7FM/DryNoMore/server/telegram_bot/src/telegram_bot.cpp

#include <iostream>
#include <tgbot/tgbot.h> // https://github.com/reo7sp/tgbot-cpp
#include <vector>

#include "telegram_bot.hpp"
#include "telegram_bot_keyboards.hpp"
#include "telegram_bot_utils.hpp"

void runDryNoMoreTelegramBot(const std::string &token,
                             const std::set<std::int64_t> &userWhitelist,
                             std::set<std::int64_t> &broadcastChats,
                             StateWrapper &state, ts_queue<Message> &msgQueue,
                             const std::atomic<bool> &running) {
  TgBot::Bot bot(token);

  std::vector<TgBot::BotCommand::Ptr> commands;
  std::vector<TgBot::EventBroadcaster::MessageListener> commandHandler;

  Settings settingSnapshot;
  auto &api = bot.getApi();

  auto addCommand = [&](const std::string &command,
                        const std::string &description,
                        TgBot::EventBroadcaster::MessageListener handler) {
    TgBot::BotCommand::Ptr cmd(new TgBot::BotCommand);
    cmd->command = command;
    cmd->description = description;
    commands.push_back(std::move(cmd));
    commandHandler.push_back(std::move(handler));
  };

  addCommand("start", "init conversation", [&](TgBot::Message::Ptr message) {
    api.sendMessage(message->chat->id, "Howdy!");
  });

  KeyboardManager menus(settingSnapshot, [&settingSnapshot, &state]() {
    auto &set = state.settingsWrap;
    std::scoped_lock lock(set.mut);
    // Move snapshot settings to actual settings!
    std::memcpy(&set.settings, &settingSnapshot, sizeof(settingSnapshot));
  });

  addCommand("edit", "edit the DryNoMore irrigation settings",
             [&](TgBot::Message::Ptr message) {
               const auto &set = state.settingsWrap;
               bool valid = false;
               {
                 std::scoped_lock lock(set.mut);
                 if ((valid = set.valid)) {
                   std::memcpy(&settingSnapshot, &set.settings,
                               sizeof(settingSnapshot));
                 }
               }

               if (valid) {
                 api.sendMessage(message->chat->id,
                                 generateSettingsTable(settingSnapshot), false,
                                 0, menus.init(), "Markdown");
               } else {
                 std::string response =
                     "Settings are not yet synchronized!\nPlease wait for the "
                     "next status report!";
                 api.sendMessage(message->chat->id, response);
               }
             });

  // Register callbacks!
  auto &broadcaster = bot.getEvents();

  for (size_t i = 0; i < commands.size(); ++i) {
    broadcaster.onCommand(
        commands[i]->command, [&, i](TgBot::Message::Ptr message) {
          if (!userWhitelist.contains(message->from->id)) {
            api.sendMessage(message->chat->id,
                            "Access denied! Go get your own bot! User ID: " +
                                std::to_string(message->from->id));
            return;
          }
          // save the chat ID!
          broadcastChats.insert(message->chat->id);

          commandHandler[i](message);
        });
  }

  menus.registerActions(api, broadcaster);

  // Set my commands
  api.setMyCommands(commands);

  TgBot::TgLongPoll longPoll(bot);
  while (running.load(std::memory_order_relaxed)) {
    // check if the status was not yet published & send update
    {
      std::unique_lock lock(state.statusWrap.mut);

      if (state.statusWrap.unpublished) {
        state.statusWrap.unpublished = false;
        Status statusCopy;
        std::memcpy(&statusCopy, &state.statusWrap.status, sizeof(statusCopy));
        lock.unlock();

        std::string statusUpdate = generateStatusTable(statusCopy);
        for (std::int64_t chat : broadcastChats) {
          api.sendMessage(chat, statusUpdate, false, 0,
                          std::make_shared<TgBot::GenericReply>(), "Markdown");
        }
      }
    }

    // send all messages in the message queue
    while (running.load(std::memory_order_relaxed) && !msgQueue.empty()) {
      if (auto msg = msgQueue.limited_wait_for_pop()) {
        const char *msgPrefix = nullptr;
        switch (msg->msgType) {
          case INFO_MSG: {
            msgPrefix = "INFO: ";
            break;
          }
          case WARN_MSG: {
            msgPrefix = "WARNING: ";
            break;
          }
          case ERR_MSG: {
            msgPrefix = "ERROR: ";
            break;
          }
          case FAILURE_MSG: {
            msgPrefix = "HARDWARE FAILURE: ";
            break;
          }
          default: {
            std::cerr << "Error invalid message in msgQueue!" << std::endl;
            continue;
          }
        }
        std::string message = msgPrefix + msg->msg;

        for (std::int64_t chat : broadcastChats) {
          api.sendMessage(chat, message, false, 0,
                          std::make_shared<TgBot::GenericReply>(), "Markdown");
        }
      }
    }

    // Handle user input
    try {
      longPoll.start();
    } catch (const TgBot::TgException &e) {
      std::cerr << "telegram bot error: " << e.what() << std::endl;
    } catch (const boost::system::system_error &wtf) {
      std::cerr << "boost system error: " << wtf.what() << std::endl;
    } catch (const std::exception &dafuq) {
      std::cerr << "std::exception: " << dafuq.what() << std::endl;
    }
  }
}
