7FM/DryNoMore/server/telegram_bot/src/telegram_bot_utils.cpp

#include <sstream>

#include "telegram_bot_utils.hpp"
#include "types.hpp"

static size_t findMaxStringLineSize(const std::string &s) {
  size_t max = 0;
  auto it = s.find('\n');
  if (it != std::string::npos) {
    max = std::max(it, findMaxStringLineSize(s.substr(it + 1)));
  } else {
    max = s.size();
  }

  return max;
}

static void printMultiLineRow(std::ostream &stream,
                              const std::vector<size_t> &maxChars,
                              const std::vector<std::string> &row,
                              const std::vector<bool> &printLeftWhitespace,
                              const std::vector<bool> &printRightWhitespace) {
  std::vector<std::string> newRow;
  std::vector<std::string> nextRow;
  const std::vector<std::string> *currentRow = &row;

  do {
    stream << "|";
    for (size_t i = 0; i < maxChars.size(); ++i) {
      if (printLeftWhitespace.empty() || printLeftWhitespace[i]) {
        stream << ' ';
      }
      auto old = stream.width(maxChars[i]);
      const auto &s = (*currentRow)[i];

      // Split up row if it contains newlines
      auto it = s.find('\n');
      if (it != std::string::npos) {
        // Fill with empty strings up to i
        newRow.resize(i);

        stream << s.substr(0, it);
        newRow.push_back(s.substr(it + 1));
      } else {
        stream << s;
      }

      stream.width(old);
      stream << (printRightWhitespace.empty() || printRightWhitespace[i] ? " |"
                                                                         : "|");
    }
    stream << '\n';

    std::swap(nextRow, newRow);
    newRow.clear();

    if (!nextRow.empty()) {
      nextRow.resize(maxChars.size());
    }
    currentRow = &nextRow;
  } while (!currentRow->empty());
}

std::string generateTable(const std::vector<std::vector<std::string>> &table,
                          const std::vector<bool> &printLeftWhitespace,
                          const std::vector<bool> &printRightWhitespace) {

  if (table.empty()) {
    return "";
  }

  std::vector<size_t> maxChars;
  maxChars.reserve(table[0].size());

  size_t totalWidth = 1;
  for (size_t i = 0; i < table[0].size(); ++i) {
    size_t max = 0;
    for (auto &row : table) {
      max = std::max(max, findMaxStringLineSize(row[i]));
    }
    totalWidth +=
        max + 1 +
        (printLeftWhitespace.empty() || printLeftWhitespace[i] ? 1 : 0) +
        (printRightWhitespace.empty() || printRightWhitespace[i] ? 1 : 0);
    maxChars.push_back(max);
  }

  std::stringstream ss;
  ss << "```\n";

  auto print_break = [&] {
    ss.width(totalWidth);
    ss.fill('-');
    ss << '-' << '\n';
    ss.fill(' ');
  };

  ss.setf(std::ios::left, std::ios::adjustfield);
  print_break();
  printMultiLineRow(ss, maxChars, table[0], printLeftWhitespace,
                    printRightWhitespace);
  print_break();
  for (size_t i = 1; i < table.size(); ++i) {
    printMultiLineRow(ss, maxChars, table[i], printLeftWhitespace,
                      printRightWhitespace);
  }
  print_break();

  ss << "```\n";
  return ss.str();
}

std::string generateWaterSettingsTable(const Settings &settings) {
  std::vector<std::vector<std::string>> table;
  table.reserve(1 + 2);

  std::vector<bool> printLeftWhitespace = {false, true, true, true, true};
  std::vector<bool> printRightWhitespace = {false, true, true, false, false};
  std::vector<std::string> row{"ID", "Min\nVal", "Max\nVal", "Warn\nThres",
                               "Empty\nThres"};
  table.push_back(std::move(row));

  for (int i = 0; i < 2; ++i) {
    row = {"W" + std::to_string(i + 1),
           std::to_string(
               settings.sensConfs[(MAX_MOISTURE_SENSOR_COUNT) + i].minValue),
           std::to_string(
               settings.sensConfs[(MAX_MOISTURE_SENSOR_COUNT) + i].maxValue),
           std::to_string(settings.waterLvlThres[i].warnThres) + " %",
           std::to_string(settings.waterLvlThres[i].emptyThres) + " %"};
    table.push_back(std::move(row));
  }

  return "Water-level Sensor Settings:\n" +
         generateTable(table, printLeftWhitespace, printRightWhitespace);
}

std::string generateMoistSettingsTable(const Settings &settings) {
  std::vector<std::vector<std::string>> table;
  table.reserve(1 + settings.numPlants);

  std::vector<bool> printLeftWhitespace = {false, true,  true,
                                           true,  false, true};
  std::vector<bool> printRightWhitespace = {false, true,  true,
                                            false, false, true};
  std::vector<std::string> row{"ID",          "Min\nVal", "Max\nVal",
                               "Moist\nGoal", "Wat\nSen", "Skp"};
  table.push_back(std::move(row));

  for (int i = 0; i < settings.numPlants; ++i) {
    uint8_t sensorIdx =
        (settings.moistSensToWaterSensBitmap[i / 8] >> (i & 7 /*aka mod 8*/)) &
        0x01;
    uint8_t skip = (settings.skipBitmap[i / 8] >> (i & 7 /*aka mod 8*/)) & 0x01;
    row = {"P" + std::to_string(i + 1),
           std::to_string(settings.sensConfs[i].minValue),
           std::to_string(settings.sensConfs[i].maxValue),
           std::to_string(settings.targetMoisture[i]) + " %",
           sensorIdx ? "W2" : "W1",
           skip ? "yes" : "no"};
    table.push_back(std::move(row));
  }

  std::string moistureSensorSettings(
      generateTable(table, printLeftWhitespace, printRightWhitespace));
  table.clear();

  printLeftWhitespace = {false, true, true, true, true};
  printRightWhitespace = {false, false, false, false, false};
  row = {"ID", "Burst\nLen", "Burst\nDelay", "Max #\nBursts", "Tick\nb/w\nWat"};
  table.push_back(std::move(row));

  for (int i = 0; i < settings.numPlants; ++i) {
    row = {"P" + std::to_string(i + 1),
           std::to_string(settings.burstDuration[i]),
           std::to_string(settings.burstDelay[i]),
           std::to_string(settings.maxBursts[i]),
           std::to_string(settings.ticksBetweenIrrigation[i])};
    table.push_back(std::move(row));
  }

  return "Moisture Sensor Settings:\n" + moistureSensorSettings +
         "Irrigation Settings:\n" +
         generateTable(table, printLeftWhitespace, printRightWhitespace);
}

std::string generateSettingsTable(const Settings &settings) {
  return (settings.hardwareFailure ? "Hardware Failure: true\n"
                                   : "Hardware Failure: false\n") +
         std::string(settings.debug ? "Debug Mode: true\n"
                                    : "Debug Mode: false\n") +
         generateMoistSettingsTable(settings) +
         generateWaterSettingsTable(settings);
}

std::string generateStatusTable(const Status &status) {
  std::vector<std::vector<std::string>> table;
  table.reserve(1 + status.numPlants);

  std::vector<std::string> row{"ID", "Moist\nBefore", "Moist\nAfter",
                               "Ticks\nsince\nwater"};
  table.push_back(std::move(row));

  for (int i = 0; i < status.numPlants; ++i) {
    row = {"P" + std::to_string(i + 1),
           (status.beforeMoistureLevels[i] != UNDEFINED_LEVEL_8
                ? std::to_string(status.beforeMoistureLevels[i])
                : "--") +
               " %",
           (status.afterMoistureLevels[i] != UNDEFINED_LEVEL_8
                ? std::to_string(status.afterMoistureLevels[i])
                : "--") +
               " %",
           std::to_string(status.ticksSinceIrrigation[i])};
    table.push_back(std::move(row));
  }

  std::string moistureSensorTable(generateTable(table));
  table.clear();

  row = {"ID", "WaterLvl\nBefore", "WaterLvl\nAfter"};
  table.push_back(std::move(row));

  for (int i = 0; i < status.numWaterSensors; ++i) {
    row = {"W" + std::to_string(i + 1),
           (status.beforeWaterLevels[i] != UNDEFINED_LEVEL_8
                ? std::to_string(status.beforeWaterLevels[i])
                : "--") +
               " %",
           (status.afterWaterLevels[i] != UNDEFINED_LEVEL_8
                ? std::to_string(status.afterWaterLevels[i])
                : "--") +
               " %"};
    table.push_back(std::move(row));
  }

  std::string waterSensorTable(generateTable(table));
  table.clear();

  row = {"ID", "Raw\nBefore", "Raw\nAfter"};
  table.push_back(std::move(row));

  for (int i = 0; i < status.numPlants; ++i) {
    row = {"P" + std::to_string(i + 1),
           (status.beforeMoistureLevelsRaw[i] != UNDEFINED_LEVEL_16
                ? std::to_string(status.beforeMoistureLevelsRaw[i])
                : "--"),
           (status.afterMoistureLevelsRaw[i] != UNDEFINED_LEVEL_16
                ? std::to_string(status.afterMoistureLevelsRaw[i])
                : "--")};
    table.push_back(std::move(row));
  }
  for (int i = 0; i < status.numWaterSensors; ++i) {
    row = {"W" + std::to_string(i + 1),
           (status.beforeWaterLevelsRaw[i] != UNDEFINED_LEVEL_16
                ? std::to_string(status.beforeWaterLevelsRaw[i])
                : "--"),
           (status.afterWaterLevelsRaw[i] != UNDEFINED_LEVEL_16
                ? std::to_string(status.afterWaterLevelsRaw[i])
                : "--")};
    table.push_back(std::move(row));
  }

  std::string rawSensorReadingsTable(generateTable(table));

  return "Plant Status:\n" + moistureSensorTable + "Water-level Status:\n" +
         waterSensorTable + "Raw Sensor Readings:\n" + rawSensorReadingsTable;
}
